ElectronicCats/CatWAN_Citizen/Firmware/read_mics4514/read_mics4514.ino

/***************************************************************************
  This is a example for the MISC4514 NO2 & CO sensor

  Designed specifically to work with the Electronic Cats MICS4514 Breakout
  ----> http://www.electroniccats.com

  Electronic Cats invests time and resources providing this open source code,
  please support Electronic Cats and open-source hardware by purchasing products
  from Electronic Cats!

  Written by Andrés Sabas & Rocio Rosales for Electronic Cats.
  BSD license, all text above must be included in any redistribution
 ***************************************************************************/
#define Serial SerialUSB

//analog read
int co=0;
int no2=0;

//Value voltaje
float vco=0;
float vno2=0;

//Value resistencia
float rco=0;
float rno2=0;

//Value Rs/Ro
float conCO=0;
float conNO2=0;

//cálculo de ppm 
double ppmCO=0;
double ppmNO2=0;

void setup() {
  //resolution analog reads
  analogReadResolution(12);
  Serial.begin(9600);
  //pre heating
  pinMode(9,OUTPUT);
  Serial.println("pre heating");
  digitalWrite(9, HIGH);
  //delay (30000);
  Serial.println("pre heating done");
  digitalWrite(9, LOW);
}

void loop() {
  
  //Get Sensor Data
  co=analogRead(A1);
  no2=analogRead(A2);
  //Convert to voltaje
  vco=(3.3*co)/4096;
  vno2=(3.3*no2)/4096;
  //Convert to resist
  rco=47000*((3.3-vco)/vco);//load resistor in red 1ohm
  rno2=((270*(3.3-vno2))/vno2);//load resistor in ox 270ohm
 //Convert to indicator concentration
  conCO= 47000/rco;
  conNO2= 270/rno2;
  //Calculo de particulas por millon 
  ppmCO=(4.4138*pow(conCO,-1.178));
  ppmNO2= ((-0.0003*(conNO2*conNO2))+(0.1626*conNO2)-0.0217);
  Serial.print("PPM CO");
  Serial.print(ppmCO);
  Serial.print("PPM NO2");
  Serial.println(ppmNO2);
 
  delay(1000);
}
